LucasCanete/GermanSmartknob/Sonstige/2.ElektronischeArchitektur/Magn_Encoder.png

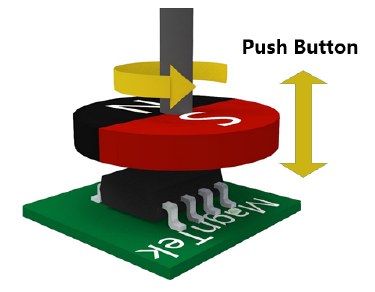
Sonstige/2.ElektronischeArchitektur/Magn_Encoder.png
