LucasCanete/GermanSmartknob/Sonstige/2.ElektronischeArchitektur/Platine_Hinterseite.png

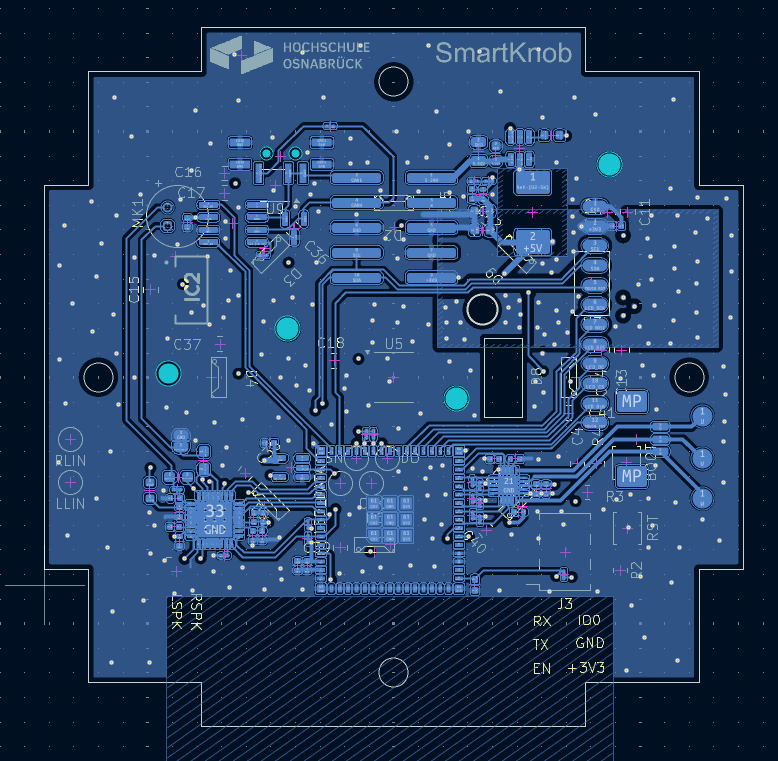
Sonstige/2.ElektronischeArchitektur/Platine_Hinterseite.png
