LucasCanete/GermanSmartknob/Sonstige/2.ElektronischeArchitektur/Platine_Vorderseite.png

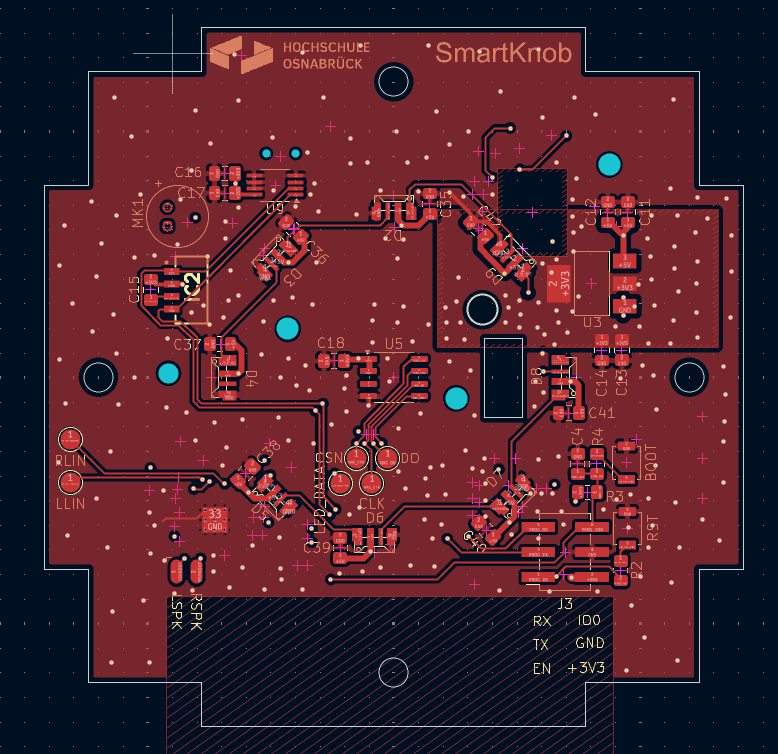
Sonstige/2.ElektronischeArchitektur/Platine_Vorderseite.png
