LucasCanete/GermanSmartknob/Sonstige/2.ElektronischeArchitektur/Screenshot_anschluesse.png

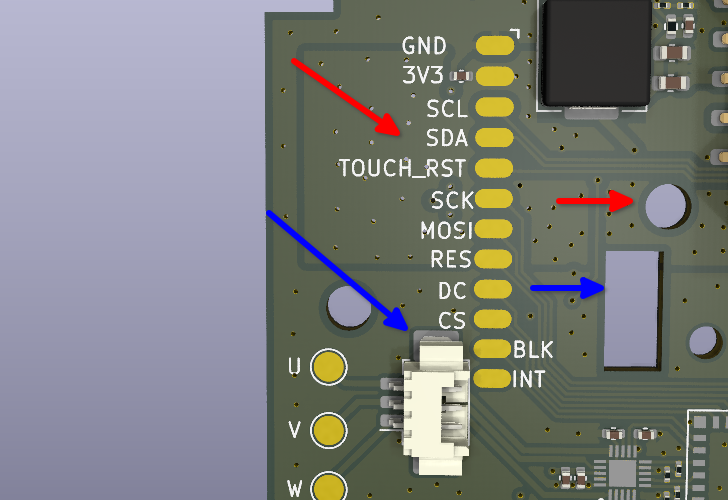
Sonstige/2.ElektronischeArchitektur/Screenshot_anschluesse.png
