LucasCanete/GermanSmartknob/Sonstige/2.ElektronischeArchitektur/screenshot_sensors.png

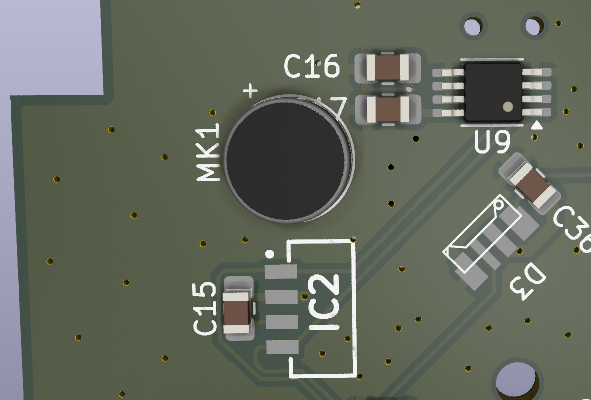
Sonstige/2.ElektronischeArchitektur/screenshot_sensors.png
