LucasCanete/GermanSmartknob/Software/audio_test/fanfare.h

unsigned char fanfare_mp3[] = {
  0x49, 0x44, 0x33, 0x04, 0x00, 0x00, 0x00, 0x00, 0x01, 0x54, 0x54, 0x44,
  0x52, 0x43, 0x00, 0x00, 0x00, 0x0c, 0x00, 0x00, 0x03, 0x32, 0x30, 0x30,
  0x38, 0x2d, 0x31, 0x30, 0x2d, 0x32, 0x35, 0x00, 0x54, 0x58, 0x58, 0x58,
  0x00, 0x00, 0x00, 0x75, 0x00, 0x00, 0x03, 0x63, 0x6f, 0x64, 0x69, 0x6e,
  0x67, 0x5f, 0x68, 0x69, 0x73, 0x74, 0x6f, 0x72, 0x79, 0x00, 0x46, 0x6f,
  0x72, 0x6d, 0x61, 0x74, 0x3d, 0x50, 0x43, 0x4d, 0x2c, 0x4d, 0x6f, 0x64,
  0x65, 0x3d, 0x53, 0x54, 0x45, 0x52, 0x45, 0x4f, 0x2c, 0x53, 0x61, 0x6d,
  0x70, 0x6c, 0x65, 0x20, 0x66, 0x72, 0x65, 0x71, 0x75, 0x65, 0x6e, 0x63,
  0x79, 0x3d, 0x34, 0x34, 0x31, 0x30, 0x30, 0x48, 0x7a, 0x2c, 0x53, 0x69,
  0x7a, 0x65, 0x20, 0x6f, 0x66, 0x20, 0x74, 0x68, 0x65, 0x20, 0x73, 0x61,
  0x6d, 0x70, 0x6c, 0x65, 0x3d, 0x31, 0x36, 0x62, 0x69, 0x74, 0x20, 0x5a,
  0x4f, 0x4f, 0x4d, 0x20, 0x48, 0x61, 0x6e, 0x64, 0x79, 0x20, 0x52, 0x65,
  0x63, 0x6f, 0x72, 0x64, 0x65, 0x72, 0x20, 0x48, 0x32, 0x20, 0x20, 0x20,
  0x20, 0x20, 0x00, 0x54, 0x58, 0x58, 0x58, 0x00, 0x00, 0x00, 0x12, 0x00,
  0x00, 0x03, 0x74, 0x69, 0x6d, 0x65, 0x5f, 0x72, 0x65, 0x66, 0x65, 0x72,
  0x65, 0x6e, 0x63, 0x65, 0x00, 0x30, 0x00, 0x54, 0x53, 0x53, 0x45, 0x00,
  0x00, 0x00, 0x0f, 0x00, 0x00, 0x03, 0x4c, 0x61, 0x76, 0x66, 0x35, 0x38,
  0x2e, 0x37, 0x36, 0x2e, 0x31, 0x30, 0x30, 0x00, 0x00, 0x00, 0x00, 0x00,
  0x00, 0x00, 0x00, 0x00, 0x00, 0x00, 0xff, 0xfb, 0x40, 0xc0, 0x00, 0x00,
  0x00, 0x00, 0x00, 0x00, 0x00, 0x00, 0x00, 0x00, 0x00, 0x00, 0x00, 0x00,
  0x00, 0x00, 0x00, 0x58, 0x69, 0x6e, 0x67, 0x00, 0x00, 0x00, 0x0f, 0x00,
  0x00, 0x00, 0x9a, 0x00, 0x01, 0x00, 0x08, 0x00, 0x05, 0x08, 0x0a, 0x0d,
  0x0f, 0x12, 0x14, 0x17, 0x19, 0x1c, 0x1e, 0x21, 0x25, 0x27, 0x2a, 0x2c,
  0x2f, 0x30, 0x33, 0x35, 0x38, 0x39, 0x3c, 0x3d, 0x40, 0x43, 0x45, 0x49,
  0x4a, 0x4d, 0x4f, 0x52, 0x54, 0x57, 0x59, 0x5c, 0x5e, 0x61, 0x64, 0x65,
  0x68, 0x6a, 0x6d, 0x6e, 0x71, 0x72, 0x76, 0x77, 0x7a, 0x7d, 0x7f, 0x82,
  0x84, 0x87, 0x88, 0x8c, 0x8d, 0x91, 0x93, 0x96, 0x98, 0x9b, 0x9e, 0x9f,
  0xa3, 0xa4, 0xa7, 0xa9, 0xaf, 0xb0, 0xb4, 0xb5, 0xbb, 0xbc, 0xc0, 0xc5,
  0xc7, 0xca, 0xcb, 0xd1, 0xd2, 0xd6, 0xd8, 0xdb, 0xdc, 0xdf, 0xe1, 0xe4,
  0xe7, 0xe9, 0xec, 0xed, 0xf1, 0xf2, 0xf5, 0xf7, 0xfa, 0xfc, 0xff, 0x00,
  0x00, 0x00, 0x00, 0x4c, 0x61, 0x76, 0x63, 0x35, 0x38, 0x2e, 0x31, 0x33,
  0x00, 0x00, 0x00, 0x00, 0x00, 0x00, 0x00, 0x00, 0x00, 0x00, 0x00, 0x00,
  0x24, 0x03, 0xf9, 0x00, 0x00, 0x00, 0x00, 0x00, 0x01, 0x00, 0x08, 0xc1,
  0x09, 0x06, 0xdc, 0x00, 0x00, 0x00, 0x00, 0x00, 0xff, 0xfb, 0xb0, 0xc4,
  0x00, 0x00, 0x05, 0xb8, 0x01, 0x29, 0xa0, 0x00, 0x00, 0x21, 0xae, 0x96,
  0xe7, 0xb4, 0xf3, 0x0e, 0x14, 0x20, 0x00, 0x5a, 0x37, 0xeb, 0xfe, 0xb6,
  0xc0, 0xa0, 0x19, 0x01, 0x30, 0x00, 0xf8, 0xb4, 0x83, 0xae, 0xcf, 0x97,
  0x7e, 0xb1, 0xc4, 0xca, 0x34, 0x6b, 0xf3, 0xe9, 0xc1, 0xf5, 0x3a, 0xe9,
  0x0f, 0x50, 0x62, 0x5c, 0x1f, 0xfc, 0x4e, 0xfe, 0x0f, 0xe1, 0x8f, 0xf5,
  0x3e, 0x43, 0xa5, 0xb3, 0x9e, 0x80, 0x34, 0xd5, 0xff, 0x7f, 0xbf, 0x26,
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
};
unsigned int fanfare_mp3_len = 65766;
